Barsy-Barsevich/Barsotion-AH4/Photos/IMG_0620.JPG

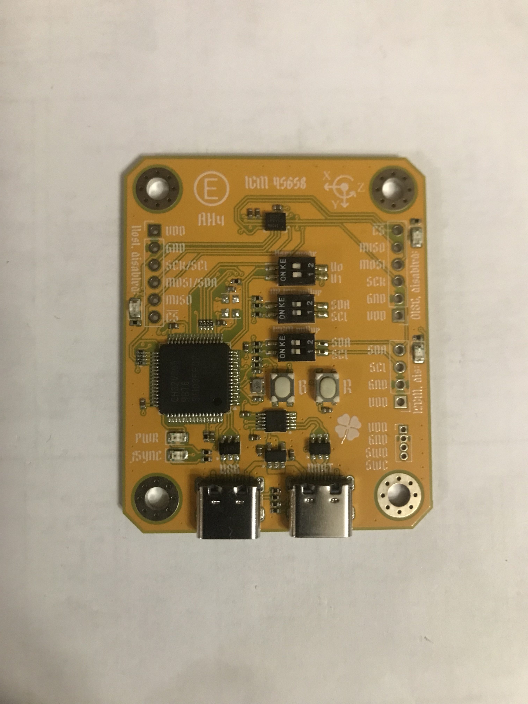
Photos/IMG_0620.JPG
