Barsy-Barsevich/Barsotion-AH4/Photos/IMG_0987.JPG

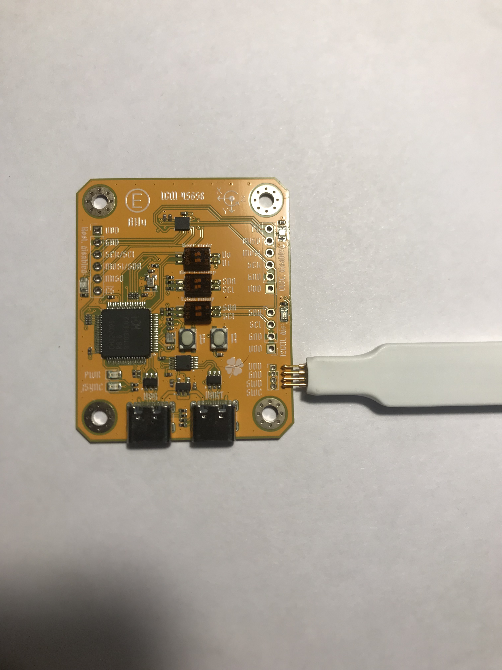
Photos/IMG_0987.JPG
