Barsy-Barsevich/Barsotion-AH4/Photos/IMG_1004.JPG

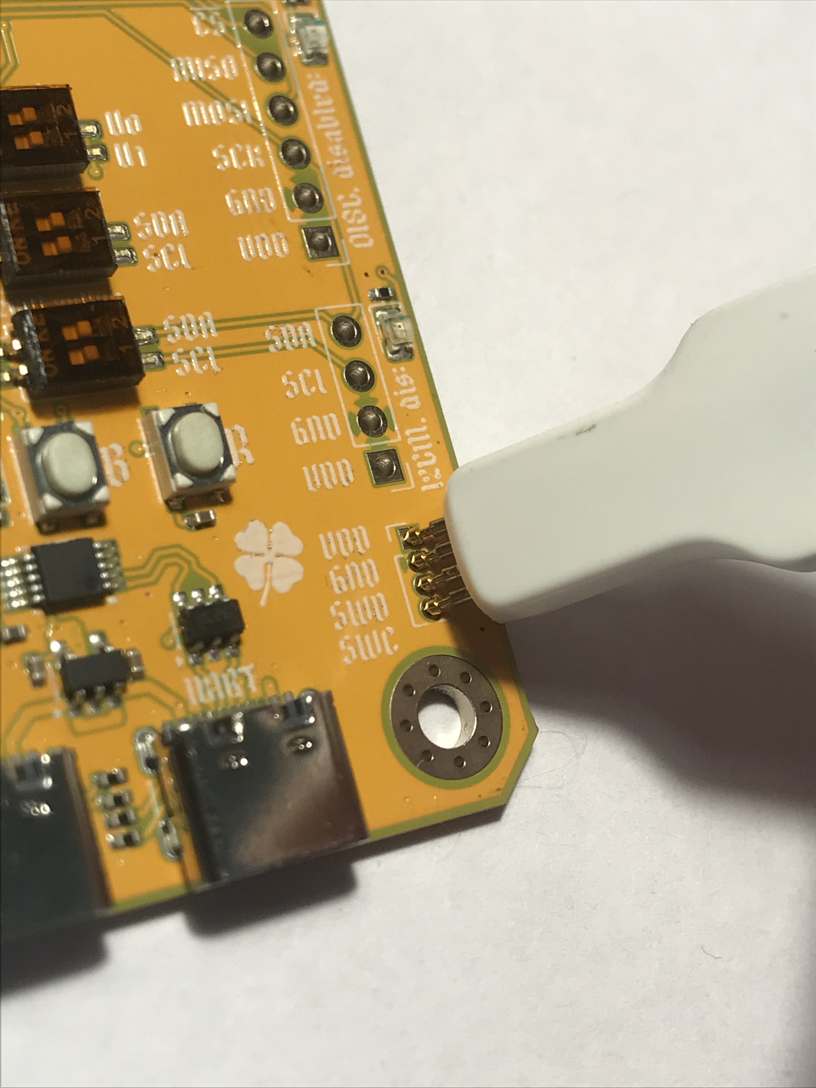
Photos/IMG_1004.JPG
