Barsy-Barsevich/Barsotion-AH4/Photos/photo_2025-10-25_11-44-28.jpg

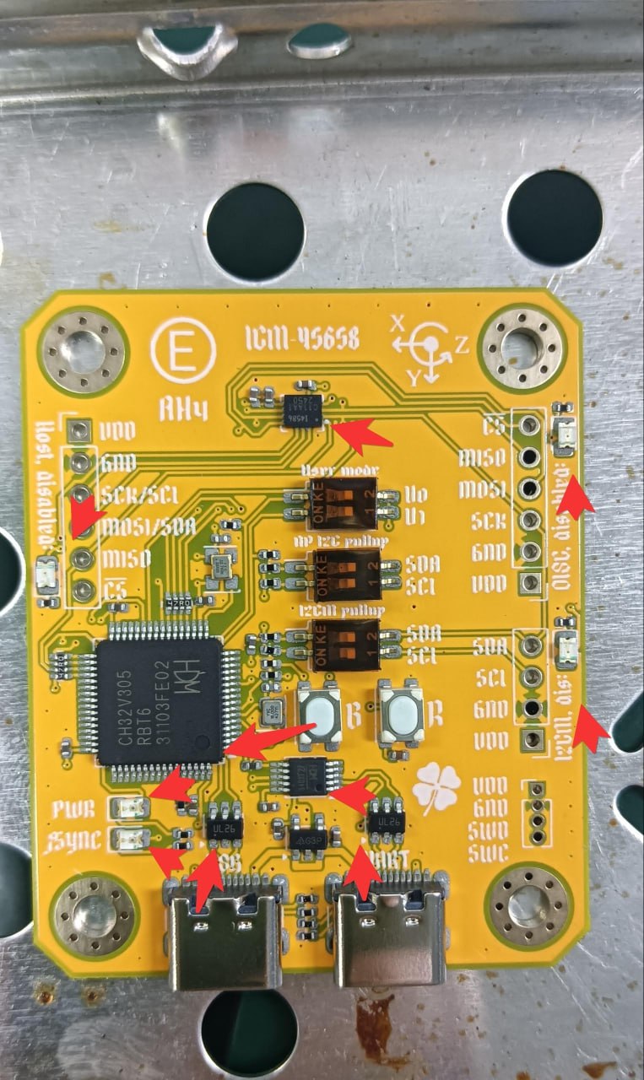
Photos/photo_2025-10-25_11-44-28.jpg
