Barsy-Barsevich/Barsotion-AH4/References/CH32V307V_EVT_R0.png

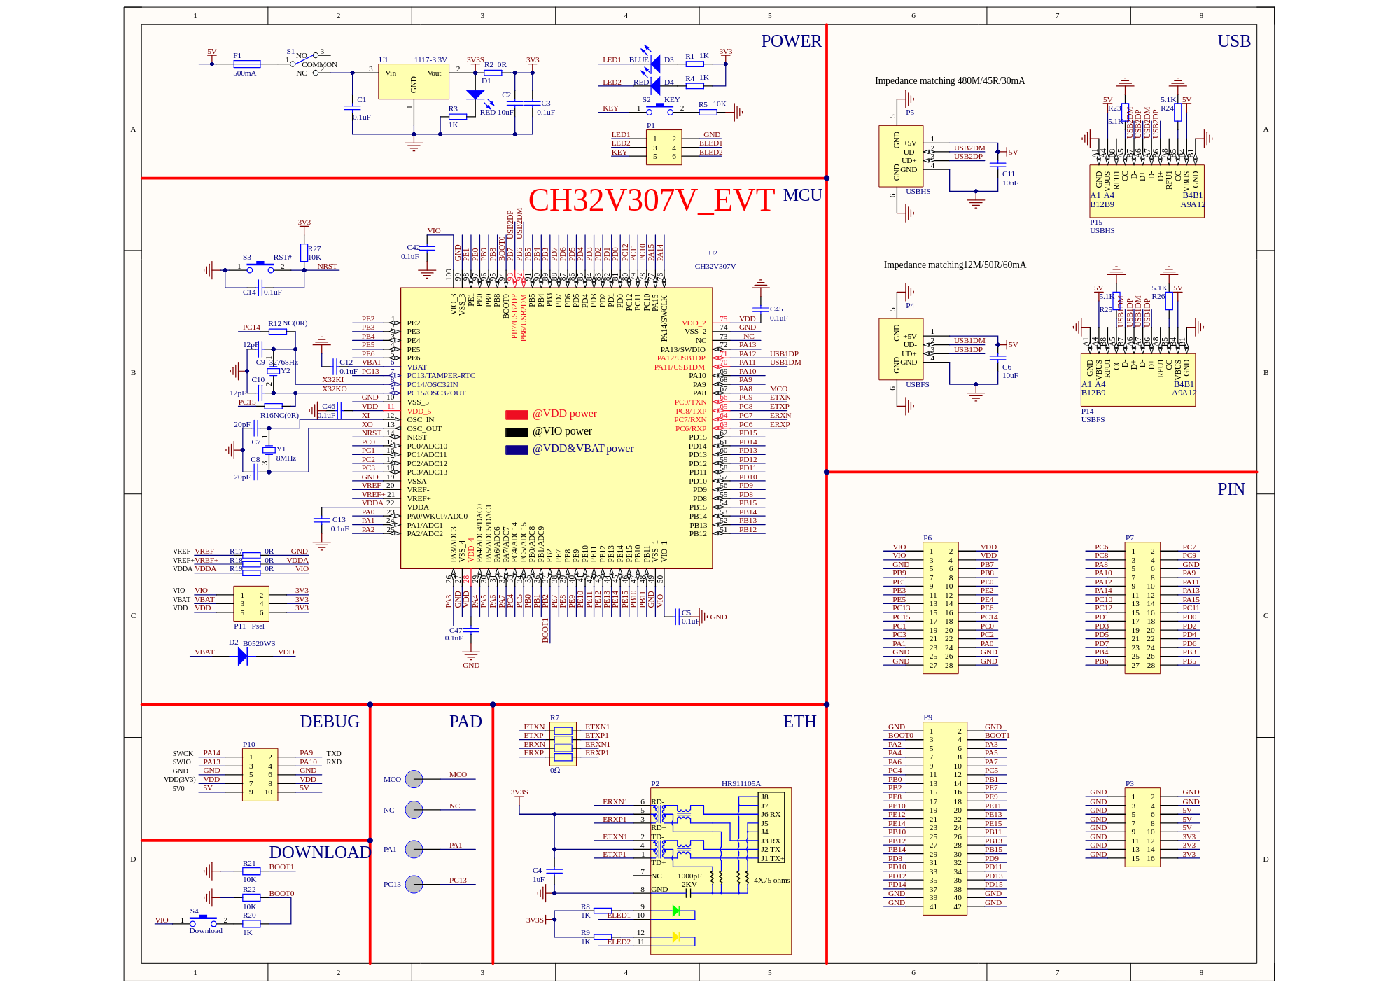
References/CH32V307V_EVT_R0.png
