Barsy-Barsevich/Barsotion-AH4/References/CH32V307V_EVT_R1.png

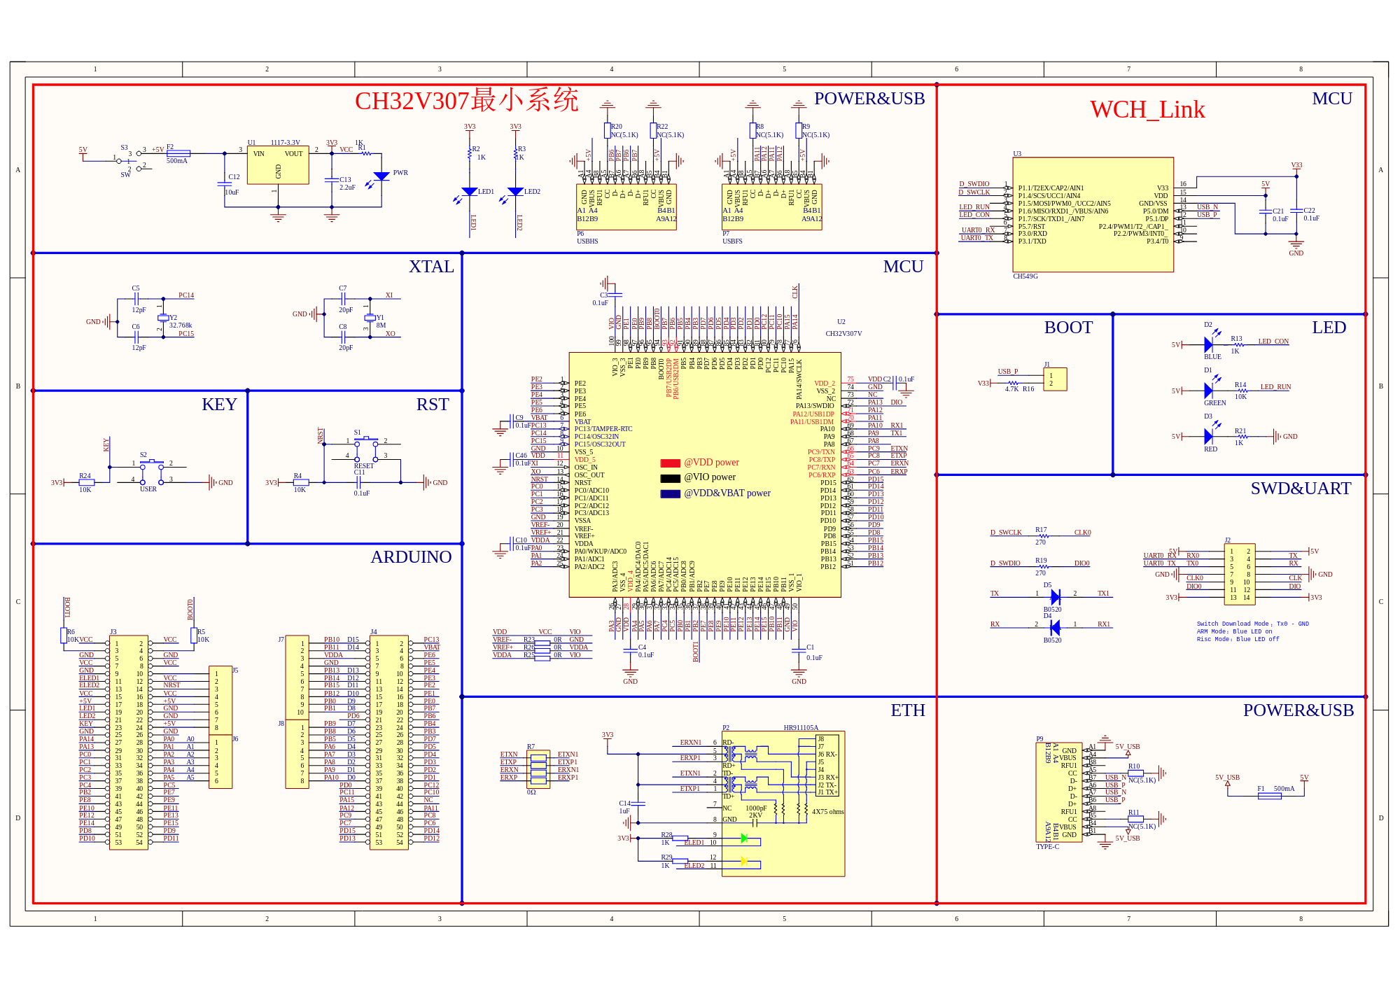
References/CH32V307V_EVT_R1.png
